David-EIPI/stm32-zigbee-light/firmware/STM32_WPAN/App/app_zigbee.c

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

/* Includes ------------------------------------------------------------------*/
#include "app_common.h"
#include "app_entry.h"
#include "dbg_trace.h"
#include "app_zigbee.h"
#include "zigbee_interface.h"
#include "shci.h"
#include "stm_logging.h"
#include "app_conf.h"
#include "stm32wbxx_core_interface_def.h"
#include "zigbee_types.h"
#include "stm32_seq.h"

#include <assert.h>
#include "zcl/zcl.h"
#include "zcl/general/zcl.temp.meas.h"
#include "zcl/general/zcl.illum.meas.h"

/* USER CODE BEGIN Includes */
#include "zcl.basic.h"
#include "main.h"
#include "hw_flash.h"
#include "ee.h"

#include "main.h"

#include "../../basic/analog.h"
#include "../../basic/binsensor.h"
#include "../../basic/multistate.h"

/* USER CODE END Includes */

#define APP_ZIGBEE_STARTUP_FAIL_DELAY               500U
#define CHANNEL                                     25

#define SW1_ENDPOINT                                1
#define SW2_ENDPOINT                                2
#define SW3_ENDPOINT                                3
#define SW4_ENDPOINT                                4
#define SW5_ENDPOINT                                5
#define SW6_ENDPOINT                                6

/* Temperature_meas (endpoint 1) specific defines ------------------------------------------------*/
#define TEMP_MIN_1                      -2000
#define TEMP_MAX_1                      5000
#define TEMP_TOLERANCE_1                      200
/* USER CODE BEGIN Temperature_meas (endpoint 1) defines */
/* USER CODE END Temperature_meas (endpoint 1) defines */

/* Illuminance_meas (endpoint 1) specific defines ------------------------------------------------*/
#define ILLUM_MIN_1                      1
#define ILLUM_MAX_1                      65534
/* USER CODE BEGIN Illuminance_meas (endpoint 1) defines */
/* USER CODE END Illuminance_meas (endpoint 1) defines */

/* USER CODE BEGIN PD */
#define CFG_NVM                 1U /* use FLASH */
#define RESET_ZB_NWK            0U

#define APP_ZIGBEE_STARTUP_REJOIN_DELAY               5000U

#define APP_ZIGBEE_REJOIN_ATTEMPTS_MAX                 2U
#define APP_ZIGBEE_TC_REJOIN_COOLDOWN_MS                60000U
#define APP_ZIGBEE_PERSIST_TIMEOUT_MS                   100000U
#define APP_ZIGBEE_DIAG_MAGIC                          0x5a424447UL /* "ZBDG" */
#define APP_ZIGBEE_DIAG_VERSION                        1U
#define APP_ZIGBEE_DIAG_WORDS                          16U
#define APP_ZIGBEE_DIAG_START_ADDR                     (CFG_EE_BANK0_MAX_NB - APP_ZIGBEE_DIAG_WORDS)
#define APP_ZIGBEE_PERSIST_CAPACITY                    ((APP_ZIGBEE_DIAG_START_ADDR * 4U) - ST_PERSIST_FLASH_DATA_OFFSET)

/* USER CODE END PD */

/* USER CODE BEGIN PM */

/* Our device is not configured as a sleepy end device, but CubeIDE still removes RXONDILE from the network setup.
 * When removed, this flag does not allow RX in idle state making Zigbee device slow to respond.
 * This macro re-definition neutralizes the auto-generated code and leaves RX always enabled.
 *
 * This hack allows to keep the project connected to the IOC file.
 *  */

#undef MCP_ASSOC_CAP_RXONIDLE
#define MCP_ASSOC_CAP_RXONIDLE 0

/*
 * Replacing the auto-generated macro with the hack below expands the channel list to all 2.4GHz channels.
 * As with the MCP_ASSOC_CAP_RXONIDLE, this hack is used to keep connection to the IOC project file.
 *  */
#undef CHANNEL
#define CHANNEL  1 ? (((1 << (26-11+1))-1) << 11) : 0
/* USER CODE END PM */

/* External definition -------------------------------------------------------*/
enum ZbStatusCodeT ZbStartupWait(struct ZigBeeT *zb, struct ZbStartupT *config);

static void APP_ZIGBEE_StackLayersInit(void);
static void APP_ZIGBEE_ConfigEndpoints(void);
static void APP_ZIGBEE_NwkForm(void);

static void APP_ZIGBEE_TraceError(const char *pMess, uint32_t ErrCode);
static void APP_ZIGBEE_CheckWirelessFirmwareInfo(void);

static void Wait_Getting_Ack_From_M0(void);
static void Receive_Ack_From_M0(void);
static void Receive_Notification_From_M0(void);

static void APP_ZIGBEE_ProcessNotifyM0ToM4(void);
static void APP_ZIGBEE_ProcessRequestM0ToM4(void);

/* USER CODE BEGIN PFP */

enum ZclStatusCodeT multistate_presentValue_CB(struct ZbZclClusterT *clusterPtr, struct ZbZclAttrCbInfoT *info);
enum ZclStatusCodeT analog_presentValue_CB(struct ZbZclClusterT *clusterPtr, struct ZbZclAttrCbInfoT *info, void *arg);

static void APP_ZIGBEE_setup_filter(void);
static void APP_ZIGBEE_ConfigBasic(void);

void set_default_attr_values(void);

static bool APP_ZIGBEE_persist_load(void);
static bool APP_ZIGBEE_persist_save(void);
static void APP_ZIGBEE_persist_delete(void);
static void APP_ZIGBEE_persist_notify_cb(struct ZigBeeT *zb, void *cbarg);
static enum ZbStatusCodeT APP_ZIGBEE_ZbStartupPersist(struct ZigBeeT *zb);
static void APP_ZIGBEE_PersistCompleted_callback(enum ZbStatusCodeT status,void *arg);
static void APP_ZIGBEE_RecoveryTask(void);
static void APP_ZIGBEE_request_recovery(uint32_t event);
static void APP_ZIGBEE_request_trust_center_rejoin(void);
static void APP_ZIGBEE_TrustCenterRejoinCompleted_callback(enum ZbStatusCodeT status, void *arg);
static void APP_ZIGBEE_mark_joined(void);
static void APP_ZIGBEE_start_coordinator_probe(void);
static void APP_ZIGBEE_CoordinatorProbeCompleted_callback(struct ZbZdoNodeDescRspT *rsp, void *arg);
static void APP_ZIGBEE_diag_record(uint32_t event, uint32_t status, uint16_t short_addr);
static bool APP_ZIGBEE_diag_load(void);
static bool APP_ZIGBEE_diag_save(void);
static uint32_t APP_ZIGBEE_crc32_update(uint32_t crc, const void *data, size_t len);


#ifdef CFG_NVM
static void APP_ZIGBEE_NVM_Init(void);
static bool APP_ZIGBEE_NVM_Read(void);
static bool APP_ZIGBEE_NVM_Write(void);
static void APP_ZIGBEE_NVM_Erase(void);
#endif /* CFG_NVM */
/* USER CODE END PFP */

static TL_CmdPacket_t   *p_ZIGBEE_otcmdbuffer;
static TL_EvtPacket_t   *p_ZIGBEE_notif_M0_to_M4;
static TL_EvtPacket_t   *p_ZIGBEE_request_M0_to_M4;
static __IO uint32_t    CptReceiveNotifyFromM0 = 0;
static __IO uint32_t    CptReceiveRequestFromM0 = 0;

PLACE_IN_SECTION("MB_MEM1") ALIGN(4) static TL_ZIGBEE_Config_t ZigbeeConfigBuffer;
PLACE_IN_SECTION("MB_MEM2") ALIGN(4) static TL_CmdPacket_t ZigbeeOtCmdBuffer;
PLACE_IN_SECTION("MB_MEM2") ALIGN(4) static uint8_t ZigbeeNotifRspEvtBuffer[sizeof(TL_PacketHeader_t) + TL_EVT_HDR_SIZE + 255U];
PLACE_IN_SECTION("MB_MEM2") ALIGN(4) static uint8_t ZigbeeNotifRequestBuffer[sizeof(TL_PacketHeader_t) + TL_EVT_HDR_SIZE + 255U];

struct zigbee_app_info
{
  bool has_init;
  struct ZigBeeT *zb;
  enum ZbStartType startupControl;
  enum ZbStatusCodeT join_status;
  uint32_t join_delay;
  bool init_after_join;

  struct ZbZclClusterT *temperature_meas_server_1;
  struct ZbZclClusterT *illuminance_meas_server_1;
};
static struct zigbee_app_info zigbee_app_info;

/* USER CODE BEGIN PV */

/* NVM variables */

static unsigned int persistNumWrites = 0;

enum app_zigbee_recovery_state {
	APP_ZIGBEE_RECOVERY_BOOT,
	APP_ZIGBEE_RECOVERY_PERSIST_PENDING,
	APP_ZIGBEE_RECOVERY_JOINED,
	APP_ZIGBEE_RECOVERY_PROBE_PENDING,
	APP_ZIGBEE_RECOVERY_REJOIN_REQUESTED,
	APP_ZIGBEE_RECOVERY_REJOIN_PENDING,
	APP_ZIGBEE_RECOVERY_FRESH_JOIN_REQUESTED,
	APP_ZIGBEE_RECOVERY_FRESH_JOIN_PENDING,
	APP_ZIGBEE_RECOVERY_TC_REJOIN_REQUESTED,
	APP_ZIGBEE_RECOVERY_TC_REJOIN_PENDING,
};

enum app_zigbee_diag_event {
	APP_ZIGBEE_DIAG_NONE,
	APP_ZIGBEE_DIAG_PERSIST_ACCEPTED,
	APP_ZIGBEE_DIAG_PERSIST_COMPLETE,
	APP_ZIGBEE_DIAG_PERSIST_FAILED,
	APP_ZIGBEE_DIAG_LEAVE,
	APP_ZIGBEE_DIAG_NETWORK_STATUS,
	APP_ZIGBEE_DIAG_REJOIN_STARTED,
	APP_ZIGBEE_DIAG_REJOIN_COMPLETE,
	APP_ZIGBEE_DIAG_FRESH_JOIN_STARTED,
	APP_ZIGBEE_DIAG_FRESH_JOIN_COMPLETE,
	APP_ZIGBEE_DIAG_PROBE_STARTED,
	APP_ZIGBEE_DIAG_PROBE_COMPLETE,
	APP_ZIGBEE_DIAG_TC_REJOIN_STARTED,
	APP_ZIGBEE_DIAG_TC_REJOIN_COMPLETE,
};

struct app_zigbee_diag_record {
	uint32_t magic;
	uint32_t version;
	uint32_t sequence;
	uint32_t last_event;
	uint32_t last_status;
	uint32_t last_short_addr;
	uint32_t persist_failures;
	uint32_t leave_events;
	uint32_t network_status_events;
	uint32_t recovery_attempts;
	uint32_t successful_recoveries;
	uint32_t last_persist_status;
	uint32_t last_leave_short_addr;
	uint32_t last_network_status;
	uint32_t last_network_short_addr;
	uint32_t crc32;
};

static struct app_zigbee_diag_record zigbee_diag;
static enum app_zigbee_recovery_state recovery_state = APP_ZIGBEE_RECOVERY_BOOT;
static bool persist_record_present;
static bool persist_record_valid;
static bool nvm_ready;
static bool diag_dirty;
static bool persist_reference_valid;
static uint16_t persist_reference_words;
static unsigned int persistNumWordsWritten;
static uint8_t rejoin_attempts;
static uint8_t trust_center_rejoin_attempts;
static uint32_t last_trust_center_rejoin_tick;
static uint64_t local_extended_address;

/* cache in uninit RAM to store/retrieve persistent data */
union cache
{
  uint8_t  U8_data[ST_PERSIST_MAX_ALLOC_SZ];     // in bytes
  uint32_t U32_data[ST_PERSIST_MAX_ALLOC_SZ/4U]; // in U32 words
};

union cache cache_persistent_data;
union cache cache_diag_reference;


struct ZbZclClusterT * analog_clusters[SW6_ENDPOINT];
struct ZbZclClusterT * multistate_cluster;
struct ZbZclClusterT * binary_cluster_light_on;
struct ZbZclClusterT * binary_cluster_motion_detect;
struct ZbZclClusterT * binary_cluster_dusk_detect;

const char *opmode_state_text[] = {
		"Auto",
		"Full",
		"Dim",
		"Off"
};

struct analog_cluster_attr {
	float value;
	float minPresent, maxPresent;
	float step;
	char desc[16];
	enum analog_mode mode;
	uint16_t engUnit;
	uint16_t icon;
	int32_t *extSetting;
	void (*ext_setting_cb)(int32_t *value);
} analog_cluster_attrs[] = {
		{
				.mode = ANALOG_OUTPUT,
				.desc = "\x09" "Dim level",
				.value = 50.0,
				.minPresent = 1.0,
				.maxPresent = 100.0,
				.step = 1.0,
				.engUnit = ZCL_ENGINEERING_UNIT_PERCENT,
				.icon = ZCL_ANALOG_ICON_BRIGHTNESS_PERCENT,
				.extSetting = &dimLevel,
		},
		{
				.mode = ANALOG_OUTPUT,
				.desc = "\x0a" "Dusk level",
				.value = 70.0,
				.minPresent = 1.0,
				.maxPresent = 200.0,
				.step = 1.0,
				.engUnit = ZCL_ENGINEERING_UNIT_PERCENT,
				.icon = ZCL_ANALOG_ICON_BRIGHTNESS_PERCENT,
				.extSetting = &ambientThreshold,
		},
		{
				.mode = ANALOG_OUTPUT,
				.desc = "\x0d" "Motion detect",
				.value = 80.0,
				.minPresent = 0.0,
				.maxPresent = 100.0,
				.step = 1.0,
				.engUnit = ZCL_ENGINEERING_UNIT_PERCENT,
				.icon = ZCL_ANALOG_ICON_PERCENT,
				.extSetting = &motionSensitivity,
				.ext_setting_cb = update_motion_sensitivity,
		},
		{
				.mode = ANALOG_OUTPUT,
				.desc = "\x0c" "After motion",
				.value = 300.0,
				.minPresent = 0.0,
				.maxPresent = 2*3600.0,
				.step = 1.0,
				.engUnit = ZCL_ENGINEERING_UNIT_SECONDS,
				.icon = ZCL_ANALOG_ICON_TIMER,
				.extSetting = &motionLight,
		},
		{
				.mode = ANALOG_OUTPUT,
				.desc = "\x0c" "After dusk",
				.value = 0.0,
				.minPresent = 1.0,
				.maxPresent = 12*60.0,
				.step = 1.0,
				.engUnit = ZCL_ENGINEERING_UNIT_MINUTES,
				.icon = ZCL_ANALOG_ICON_TIMER,
				.extSetting = &nightLight,
		},
		{
				.mode = ANALOG_OUTPUT,
				.desc = "\x0d" "Phase correct",
				.value = -300,
				.minPresent = -10000.0,
				.maxPresent = 10000,
				.step = 1,
				.engUnit = ZCL_ENGINEERING_UNIT_MICROSECONDS,
				.icon = ZCL_ANALOG_ICON_TIMER,
				.extSetting = &phase_correction,
		},
};

/* Stored attributes' values */
static uint8_t lightState = 0;
static uint8_t motionState = 0;
static uint8_t duskState = 0;

/* Data block for NVM storage */
struct persistence_attrs_v1 {
	uint32_t struct_len;
	float analogValues[lengthof(analog_cluster_attrs)];
	uint32_t multistateValue;
};

struct persistence_attrs {
	uint32_t struct_len;
	uint32_t crc32;
	float analogValues[lengthof(analog_cluster_attrs)];
	uint32_t multistateValue;
};



/* USER CODE END PV */
/* Functions Definition ------------------------------------------------------*/

/**
 * @brief  Zigbee application initialization
 * @param  None
 * @retval None
 */
void APP_ZIGBEE_Init(void)
{
  SHCI_CmdStatus_t ZigbeeInitStatus;

  APP_DBG("APP_ZIGBEE_Init");

  /* Check the compatibility with the Coprocessor Wireless Firmware loaded */
  APP_ZIGBEE_CheckWirelessFirmwareInfo();

  /* Register cmdbuffer */
  APP_ZIGBEE_RegisterCmdBuffer(&ZigbeeOtCmdBuffer);

  /* Init config buffer and call TL_ZIGBEE_Init */
  APP_ZIGBEE_TL_INIT();

  /* Register task */
  /* Create the different tasks */
  UTIL_SEQ_RegTask(1U << (uint32_t)CFG_TASK_NOTIFY_FROM_M0_TO_M4, UTIL_SEQ_RFU, APP_ZIGBEE_ProcessNotifyM0ToM4);
  UTIL_SEQ_RegTask(1U << (uint32_t)CFG_TASK_REQUEST_FROM_M0_TO_M4, UTIL_SEQ_RFU, APP_ZIGBEE_ProcessRequestM0ToM4);

  /* Task associated with network creation process */
  UTIL_SEQ_RegTask(1U << CFG_TASK_ZIGBEE_NETWORK_FORM, UTIL_SEQ_RFU, APP_ZIGBEE_NwkForm);

  /* USER CODE BEGIN APP_ZIGBEE_INIT */
//  UTIL_SEQ_RegTask(1U << CFG_TASK_ZIGBEE_NETWORK_REJOIN, UTIL_SEQ_RFU, APP_ZIGBEE_NwkRejoin);
  UTIL_SEQ_RegTask(1U << CFG_TASK_ZIGBEE_RECOVERY, UTIL_SEQ_RFU, APP_ZIGBEE_RecoveryTask);

  /* NVM Init */
#if CFG_NVM
  APP_ZIGBEE_NVM_Init();
#endif

  /* USER CODE END APP_ZIGBEE_INIT */

  /* Start the Zigbee on the CPU2 side */
  ZigbeeInitStatus = SHCI_C2_ZIGBEE_Init();
  /* Prevent unused argument(s) compilation warning */
  UNUSED(ZigbeeInitStatus);

  /* Initialize Zigbee stack layers */
  APP_ZIGBEE_StackLayersInit();

}

/**
 * @brief  Initialize Zigbee stack layers
 * @param  None
 * @retval None
 */
static void APP_ZIGBEE_StackLayersInit(void)
{
  APP_DBG("APP_ZIGBEE_StackLayersInit");

  zigbee_app_info.zb = ZbInit(0U, NULL, NULL);
  assert(zigbee_app_info.zb != NULL);

  /* Create the endpoint and cluster(s) */
  APP_ZIGBEE_ConfigEndpoints();

  /* USER CODE BEGIN APP_ZIGBEE_StackLayersInit */
  zigbee_app_info.join_status = (enum ZbStatusCodeT) 0x01; /* init to error status */
  APP_ZIGBEE_setup_filter();
  local_extended_address = ZbExtendedAddress(zigbee_app_info.zb);

  /* STEP 1 - TRY to START FROM PERSISTENCE */
  enum ZbStatusCodeT status;

  /* First we disable the persistent notification */
  ZbPersistNotifyRegister(zigbee_app_info.zb,NULL,NULL);

  /* Increase transmission power (to 3.7dbm). Default setting is 0. */
  ZbNwkIfSetTxPower(zigbee_app_info.zb, "wpan0", 6);
  enum ZbStatusCodeT res;

  /* Remove parent link strength threshold. This application does not transmit frequent data
   * and association happens faster when more nodes are available.  */
  uint32_t bdb_flags = 0;
  res = ZbBdbGetIndex(zigbee_app_info.zb, ZB_BDB_Flags, &bdb_flags, sizeof(bdb_flags), 0);
  if (ZB_STATUS_SUCCESS == res) {
	  bdb_flags |= ZB_BDB_FLAG_IGNORE_COST_DURING_JOIN;
	  (void)ZbBdbSetIndex(zigbee_app_info.zb, ZB_BDB_Flags, &bdb_flags, sizeof(bdb_flags), 0);
  }


  /* Call a startup from persistence */
#if CFG_NVM
#if (RESET_ZB_NWK)
  APP_ZIGBEE_persist_delete();
#endif
#endif

  status = APP_ZIGBEE_ZbStartupPersist(zigbee_app_info.zb);
  if(status == ZB_STATUS_SUCCESS)
  {
     /* The return value only means that CPU2 accepted the asynchronous request.
      * Network state is marked joined by APP_ZIGBEE_PersistCompleted_callback(). */
     APP_DBG("ZbStartupPersist: request accepted; waiting for completion");
     recovery_state = APP_ZIGBEE_RECOVERY_PERSIST_PENDING;
     zigbee_app_info.has_init = true;
     APP_ZIGBEE_diag_record(APP_ZIGBEE_DIAG_PERSIST_ACCEPTED, status, 0xffffU);
     return;
  }
  else
  {
       APP_DBG("ZbStartupPersist: request rejected with status: 0x%02x",status);
       if (persist_record_present) {
         APP_ZIGBEE_diag_record(APP_ZIGBEE_DIAG_PERSIST_FAILED, status, 0xffffU);
         APP_ZIGBEE_request_recovery(APP_ZIGBEE_DIAG_PERSIST_FAILED);
         zigbee_app_info.has_init = true;
         return;
       }
  }
  /* USER CODE END APP_ZIGBEE_StackLayersInit */

  /* Configure the joining parameters */
  zigbee_app_info.join_status = (enum ZbStatusCodeT) 0x01; /* init to error status */
  zigbee_app_info.join_delay = HAL_GetTick(); /* now */
  zigbee_app_info.startupControl = ZbStartTypeJoin;

  /* Initialization Complete */
  zigbee_app_info.has_init = true;

  /* run the task */
  UTIL_SEQ_SetTask(1U << CFG_TASK_ZIGBEE_NETWORK_FORM, CFG_SCH_PRIO_0);
}

/**
 * @brief  Configure Zigbee application endpoints
 * @param  None
 * @retval None
 */
static void APP_ZIGBEE_ConfigEndpoints(void)
{
  struct ZbApsmeAddEndpointReqT req;
  struct ZbApsmeAddEndpointConfT conf;

  memset(&req, 0, sizeof(req));

  /* Endpoint: SW1_ENDPOINT */
  req.profileId = ZCL_PROFILE_HOME_AUTOMATION;
  req.deviceId = ZCL_DEVICE_LEVEL_OUTPUT;
  req.endpoint = SW1_ENDPOINT;
  ZbZclAddEndpoint(zigbee_app_info.zb, &req, &conf);
  assert(conf.status == ZB_STATUS_SUCCESS);

  /* Temperature meas server */
  zigbee_app_info.temperature_meas_server_1 = ZbZclTempMeasServerAlloc(zigbee_app_info.zb, SW1_ENDPOINT, TEMP_MIN_1, TEMP_MAX_1, TEMP_TOLERANCE_1);
  assert(zigbee_app_info.temperature_meas_server_1 != NULL);
  ZbZclClusterEndpointRegister(zigbee_app_info.temperature_meas_server_1);
  /* Illuminance meas server */
  zigbee_app_info.illuminance_meas_server_1 = ZbZclIllumMeasServerAlloc(zigbee_app_info.zb, SW1_ENDPOINT, ILLUM_MIN_1, ILLUM_MAX_1);
  assert(zigbee_app_info.illuminance_meas_server_1 != NULL);
  ZbZclClusterEndpointRegister(zigbee_app_info.illuminance_meas_server_1);
  /* Endpoint: SW2_ENDPOINT */
  req.profileId = ZCL_PROFILE_HOME_AUTOMATION;
  req.deviceId = ZCL_DEVICE_LEVEL_OUTPUT;
  req.endpoint = SW2_ENDPOINT;
  ZbZclAddEndpoint(zigbee_app_info.zb, &req, &conf);
  assert(conf.status == ZB_STATUS_SUCCESS);

  /* Endpoint: SW3_ENDPOINT */
  req.profileId = ZCL_PROFILE_HOME_AUTOMATION;
  req.deviceId = ZCL_DEVICE_LEVEL_OUTPUT;
  req.endpoint = SW3_ENDPOINT;
  ZbZclAddEndpoint(zigbee_app_info.zb, &req, &conf);
  assert(conf.status == ZB_STATUS_SUCCESS);

  /* Endpoint: SW4_ENDPOINT */
  req.profileId = ZCL_PROFILE_HOME_AUTOMATION;
  req.deviceId = ZCL_DEVICE_LEVEL_OUTPUT;
  req.endpoint = SW4_ENDPOINT;
  ZbZclAddEndpoint(zigbee_app_info.zb, &req, &conf);
  assert(conf.status == ZB_STATUS_SUCCESS);

  /* Endpoint: SW5_ENDPOINT */
  req.profileId = ZCL_PROFILE_HOME_AUTOMATION;
  req.deviceId = ZCL_DEVICE_LEVEL_OUTPUT;
  req.endpoint = SW5_ENDPOINT;
  ZbZclAddEndpoint(zigbee_app_info.zb, &req, &conf);
  assert(conf.status == ZB_STATUS_SUCCESS);

  /* Endpoint: SW6_ENDPOINT */
  req.profileId = ZCL_PROFILE_HOME_AUTOMATION;
  req.deviceId = ZCL_DEVICE_ONOFF_SWITCH;
  req.endpoint = SW6_ENDPOINT;
  ZbZclAddEndpoint(zigbee_app_info.zb, &req, &conf);
  assert(conf.status == ZB_STATUS_SUCCESS);

  /* USER CODE BEGIN CONFIG_ENDPOINT */
  struct zcl_msv_attr_callbacks_t cb = {
		  .msv_presentValue = multistate_presentValue_CB,
  };
  multistate_cluster = ZbZcl_msv_ServerAlloc(zigbee_app_info.zb, SW1_ENDPOINT, MULTISTATE_VALUE,
		  lengthof(opmode_state_text), opmode_state_text, &cb, NULL);
  assert(multistate_cluster != NULL);

  char *msv_desc = "\x09" "Operation";
  (void)ZbZclAttrStringWriteShort(multistate_cluster, ZCL_MULTISTATE_DESCRIPTION_ATTR, (uint8_t*)msv_desc);

  ZbZclClusterEndpointRegister(multistate_cluster);

  unsigned ep_idx;
  for (ep_idx = SW1_ENDPOINT; ep_idx <= SW6_ENDPOINT; ep_idx += 1) {
	  unsigned cl_idx = ep_idx - 1;
	  struct zcl_analog_attr_callbacks_t analog_cb = {
			  .read = NULL,
			  .write = analog_presentValue_CB,
	  };

	  analog_clusters[cl_idx] = ZbZcl_Analog_ServerAlloc(
			  zigbee_app_info.zb,
			  ep_idx,
			  analog_cluster_attrs[cl_idx].mode,
			  &analog_cluster_attrs[cl_idx].value,
			  &analog_cb,
			  &analog_cluster_attrs[cl_idx]);

	  assert(analog_clusters[cl_idx] != NULL);

	  (void)ZbZclAttrFloatWrite(analog_clusters[cl_idx], ZCL_ANALOG_PRESENT_VALUE_ATTR, analog_cluster_attrs[cl_idx].value);
	  (void)ZbZclAttrFloatWrite(analog_clusters[cl_idx], ZCL_ANALOG_MAX_PRESENT_ATTR, analog_cluster_attrs[cl_idx].maxPresent);
	  (void)ZbZclAttrFloatWrite(analog_clusters[cl_idx], ZCL_ANALOG_MIN_PRESENT_ATTR, analog_cluster_attrs[cl_idx].minPresent);
	  (void)ZbZclAttrFloatWrite(analog_clusters[cl_idx], ZCL_ANALOG_RESOLUTION_ATTR, analog_cluster_attrs[cl_idx].step);
	  (void)ZbZclAttrIntegerWrite(analog_clusters[cl_idx], ZCL_ANALOG_ENGINEERING_UNITS_ATTR, analog_cluster_attrs[cl_idx].engUnit);
	  (void)ZbZclAttrIntegerWrite(analog_clusters[cl_idx], ZCL_ANALOG_APPLICATION_TYPE_ATTR, analog_cluster_attrs[cl_idx].icon << 16);
	  (void)ZbZclAttrStringWriteShort(analog_clusters[cl_idx], ZCL_ANALOG_DESCRIPTION_ATTR, (uint8_t*)analog_cluster_attrs[cl_idx].desc);
	  ZbZclClusterEndpointRegister(analog_clusters[cl_idx]);
  }

  binary_cluster_light_on = ZbZcl_Binary_ServerAlloc(zigbee_app_info.zb, SW1_ENDPOINT, BINARY_SENSOR_INPUT,
		  &lightState, NULL, NULL);
  assert(binary_cluster_light_on != NULL);
  ZbZclClusterEndpointRegister(binary_cluster_light_on);

  uint8_t light_on_sensor_desc[] = "\x0b" "Light state";
  (void)ZbZclAttrStringWriteShort(binary_cluster_light_on, ZCL_BINARY_DESCRIPTION_ATTR, light_on_sensor_desc);


  binary_cluster_dusk_detect = ZbZcl_Binary_ServerAlloc(zigbee_app_info.zb, SW2_ENDPOINT, BINARY_SENSOR_INPUT,
		  &duskState, NULL, NULL);
  assert(binary_cluster_dusk_detect != NULL);

  ZbZclClusterEndpointRegister(binary_cluster_dusk_detect);

  uint8_t dusk_detect_sensor_desc[] = "\x0b" "Dusk detect";
  (void)ZbZclAttrStringWriteShort(binary_cluster_dusk_detect, ZCL_BINARY_DESCRIPTION_ATTR, dusk_detect_sensor_desc);

  binary_cluster_motion_detect = ZbZcl_Binary_ServerAlloc(zigbee_app_info.zb, SW3_ENDPOINT, BINARY_SENSOR_INPUT,
		  &motionState, NULL, NULL);
  assert(binary_cluster_motion_detect != NULL);

  uint8_t motion_detect_sensor_desc[] = "\x0d" "Motion detect";
  (void)ZbZclAttrStringWriteShort(binary_cluster_motion_detect, ZCL_BINARY_DESCRIPTION_ATTR, motion_detect_sensor_desc);

  ZbZclClusterEndpointRegister(binary_cluster_motion_detect);

#if (!USE_TRAILING_EDGE)
/* This section is disabled because the current triac control is not compatible with the trailing edge drive mode */
  binary_triac_mode_cluster = ZbZcl_Binary_ServerAlloc(zigbee_app_info.zb, SW1_ENDPOINT, BINARY_SENSOR_OUTPUT,
		  &trailing_edge, NULL, NULL);
  assert(binary_triac_mode_cluster != NULL);
  ZbZclClusterEndpointRegister(binary_triac_mode_cluster);

  uint8_t triac_mode_desc[] = "\x0d" "Trailing edge";
  (void)ZbZclAttrStringWriteShort(binary_triac_mode_cluster, ZCL_BINARY_DESCRIPTION_ATTR, triac_mode_desc);
#endif

  APP_ZIGBEE_ConfigBasic();
  set_default_attr_values();
  /* USER CODE END CONFIG_ENDPOINT */
}

/**
 * @brief  Handle Zigbee network forming and joining
 * @param  None
 * @retval None
 */
static void APP_ZIGBEE_NwkForm(void)
{
  if ((zigbee_app_info.join_status != ZB_STATUS_SUCCESS) && (HAL_GetTick() >= zigbee_app_info.join_delay))
  {
    struct ZbStartupT config;
    enum ZbStatusCodeT status;

    /* Configure Zigbee Logging */
    ZbSetLogging(zigbee_app_info.zb, ZB_LOG_MASK_LEVEL_5, NULL);

    /* Attempt to join a zigbee network */
    ZbStartupConfigGetProDefaults(&config);

    /* Set the centralized network */
    APP_DBG("Network config : APP_STARTUP_CENTRALIZED_ROUTER");
    config.startupControl = zigbee_app_info.startupControl;

    /* Using the default HA preconfigured Link Key */
    memcpy(config.security.preconfiguredLinkKey, sec_key_ha, ZB_SEC_KEYSIZE);

    config.channelList.count = 1;
    config.channelList.list[0].page = 0;
    config.channelList.list[0].channelMask = 1 << CHANNEL; /*Channel in use */

    /* Using ZbStartupWait (blocking) */
    status = ZbStartupWait(zigbee_app_info.zb, &config);

    APP_DBG("ZbStartup Callback (status = 0x%02x)", status);
    zigbee_app_info.join_status = status;

    if (status == ZB_STATUS_SUCCESS)
    {
      zigbee_app_info.join_delay = 0U;
      zigbee_app_info.init_after_join = true;
      APP_DBG("Startup done !\n");
      /* USER CODE BEGIN 0 */

#if CFG_NVM
      /* Register Persistent data change notification */
      ZbPersistNotifyRegister(zigbee_app_info.zb,APP_ZIGBEE_persist_notify_cb,NULL);
      /* Call the callback once here to save persistence data */
      APP_ZIGBEE_persist_notify_cb(zigbee_app_info.zb,NULL);
#endif
      recovery_state = APP_ZIGBEE_RECOVERY_JOINED;
      rejoin_attempts = 0U;
      APP_ZIGBEE_diag_record(APP_ZIGBEE_DIAG_FRESH_JOIN_COMPLETE, status, ZbShortAddress(zigbee_app_info.zb));
      zigbee_diag.successful_recoveries++;
      diag_dirty = true;
      UTIL_SEQ_SetTask(1U << CFG_TASK_ZIGBEE_RECOVERY, CFG_SCH_PRIO_0);
      ZbZclAttrReportKick(multistate_cluster, true, NULL, NULL);
      /* Use an absolute value. Multiplying the current value after every
       * recovery caused exponential growth and eventual integer overflow. */
      uint32_t pers_tm = APP_ZIGBEE_PERSIST_TIMEOUT_MS;
      (void)ZbBdbSetIndex(zigbee_app_info.zb, ZB_BDB_PersistTimeoutMs,
		      &pers_tm, sizeof(pers_tm), 0);

      /* USER CODE END 0 */
    }
    else
    {
      APP_DBG("Startup failed, attempting again after a short delay (%d ms)", APP_ZIGBEE_STARTUP_FAIL_DELAY);
      zigbee_app_info.join_delay = HAL_GetTick() + APP_ZIGBEE_STARTUP_FAIL_DELAY;
      /* USER CODE BEGIN 1 */
      if (status != ZB_NWK_STATUS_NO_NETWORKS) {
	  zigbee_app_info.join_delay = HAL_GetTick() + APP_ZIGBEE_STARTUP_REJOIN_DELAY;
      }
      if (status == ZB_NWK_STATUS_INVALID_REQUEST || ZB_APS_STATUS_SECURITY_FAIL == status) {
    	  /* Some router devices return these error codes during first join and M0 firmware becomes
    	   * unable to join after that. It keeps sending same data and receives same error code
    	   * over and over again.
    	   * Restarting the joining process with ZbReset() seems to help most of the time. */
	  ZbReset(zigbee_app_info.zb);
      }
      recovery_state = APP_ZIGBEE_RECOVERY_FRESH_JOIN_PENDING;
      APP_ZIGBEE_diag_record(APP_ZIGBEE_DIAG_FRESH_JOIN_COMPLETE, status, 0xffffU);

      /* USER CODE END 1 */
    }
  }

  /* If Network forming/joining was not successful reschedule the current task to retry the process */
  if (zigbee_app_info.join_status != ZB_STATUS_SUCCESS)
  {
    UTIL_SEQ_SetTask(1U << CFG_TASK_ZIGBEE_NETWORK_FORM, CFG_SCH_PRIO_0);
  }
  /* USER CODE BEGIN NW_FORM */
  if (diag_dirty) {
	  UTIL_SEQ_SetTask(1U << CFG_TASK_ZIGBEE_RECOVERY, CFG_SCH_PRIO_0);
  }
  /* USER CODE END NW_FORM */
}

/*************************************************************
 * ZbStartupWait Blocking Call
 *************************************************************/
struct ZbStartupWaitInfo
{
  bool active;
  enum ZbStatusCodeT status;
};

static void ZbStartupWaitCb(enum ZbStatusCodeT status, void *cb_arg)
{
  struct ZbStartupWaitInfo *info = cb_arg;

  info->status = status;
  info->active = false;
  UTIL_SEQ_SetEvt(EVENT_ZIGBEE_STARTUP_ENDED);
}

enum ZbStatusCodeT ZbStartupWait(struct ZigBeeT *zb, struct ZbStartupT *config)
{
  struct ZbStartupWaitInfo *info;
  enum ZbStatusCodeT status;

  info = malloc(sizeof(struct ZbStartupWaitInfo));
  if (info == NULL)
  {
    return ZB_STATUS_ALLOC_FAIL;
  }
  memset(info, 0, sizeof(struct ZbStartupWaitInfo));

  info->active = true;
  status = ZbStartup(zb, config, ZbStartupWaitCb, info);
  if (status != ZB_STATUS_SUCCESS)
  {
    free(info);
    return status;
  }

  UTIL_SEQ_WaitEvt(EVENT_ZIGBEE_STARTUP_ENDED);
  status = info->status;
  free(info);
  return status;
}

/**
 * @brief  Trace the error or the warning reported.
 * @param  ErrId :
 * @param  ErrCode
 * @retval None
 */
void APP_ZIGBEE_Error(uint32_t ErrId, uint32_t ErrCode)
{
  switch (ErrId)
  {
    default:
      APP_ZIGBEE_TraceError("ERROR Unknown ", 0);
      break;
  }
}

/*************************************************************
 *
 * LOCAL FUNCTIONS
 *
 *************************************************************/

/**
 * @brief  Warn the user that an error has occurred.
 *
 * @param  pMess  : Message associated to the error.
 * @param  ErrCode: Error code associated to the module (Zigbee or other module if any)
 * @retval None
 */
static void APP_ZIGBEE_TraceError(const char *pMess, uint32_t ErrCode)
{
  APP_DBG("**** Fatal error = %s (Err = %d)", pMess, ErrCode);
}

/**
 * @brief Check if the Coprocessor Wireless Firmware loaded supports Zigbee
 *        and display associated information
 * @param  None
 * @retval None
 */
static void APP_ZIGBEE_CheckWirelessFirmwareInfo(void)
{
  WirelessFwInfo_t wireless_info_instance;
  WirelessFwInfo_t *p_wireless_info = &wireless_info_instance;

  if (SHCI_GetWirelessFwInfo(p_wireless_info) != SHCI_Success)
  {
    APP_ZIGBEE_Error((uint32_t)ERR_ZIGBEE_CHECK_WIRELESS, (uint32_t)ERR_INTERFACE_FATAL);
  }
  else
  {
    APP_DBG("**********************************************************");
    APP_DBG("WIRELESS COPROCESSOR FW:");
    /* Print version */
    APP_DBG("VERSION ID = %d.%d.%d", p_wireless_info->VersionMajor, p_wireless_info->VersionMinor, p_wireless_info->VersionSub);

    switch (p_wireless_info->StackType)
    {
      case INFO_STACK_TYPE_ZIGBEE_FFD:
        APP_DBG("FW Type : FFD Zigbee stack");
        break;

      case INFO_STACK_TYPE_ZIGBEE_RFD:
        APP_DBG("FW Type : RFD Zigbee stack");
        break;

      default:
        /* No Zigbee device supported ! */
        APP_ZIGBEE_Error((uint32_t)ERR_ZIGBEE_CHECK_WIRELESS, (uint32_t)ERR_INTERFACE_FATAL);
        break;
    }

    /* print the application name */
    char *__PathProject__ = (strstr(__FILE__, "Zigbee") ? strstr(__FILE__, "Zigbee") + 7 : __FILE__);
    char *pdel = NULL;
    if((strchr(__FILE__, '/')) == NULL)
    {
      pdel = strchr(__PathProject__, '\\');
    }
    else
    {
      pdel = strchr(__PathProject__, '/');
    }

    int index = (int)(pdel - __PathProject__);
    APP_DBG("Application flashed: %*.*s", index, index, __PathProject__);

    /* print channel */
    APP_DBG("Channel used: %d", CHANNEL);
    /* print Link Key */
    APP_DBG("Link Key: %.16s", sec_key_ha);
    /* print Link Key value hex */
    char Z09_LL_string[ZB_SEC_KEYSIZE*3+1];
    Z09_LL_string[0] = 0;
    for (int str_index = 0; str_index < ZB_SEC_KEYSIZE; str_index++)
    {
      sprintf(&Z09_LL_string[str_index*3], "%02x ", sec_key_ha[str_index]);
    }

    APP_DBG("Link Key value: %s", Z09_LL_string);
    /* print clusters allocated */
    APP_DBG("Clusters allocated are:");
    APP_DBG("temperature_meas Server on Endpoint %d", SW1_ENDPOINT);
    APP_DBG("illuminance_meas Server on Endpoint %d", SW1_ENDPOINT);
    APP_DBG("**********************************************************");
  }
}

/*************************************************************
 *
 * WRAP FUNCTIONS
 *
 *************************************************************/

void APP_ZIGBEE_RegisterCmdBuffer(TL_CmdPacket_t *p_buffer)
{
  p_ZIGBEE_otcmdbuffer = p_buffer;
}

Zigbee_Cmd_Request_t * ZIGBEE_Get_OTCmdPayloadBuffer(void)
{
  return (Zigbee_Cmd_Request_t *)p_ZIGBEE_otcmdbuffer->cmdserial.cmd.payload;
}

Zigbee_Cmd_Request_t * ZIGBEE_Get_OTCmdRspPayloadBuffer(void)
{
  return (Zigbee_Cmd_Request_t *)((TL_EvtPacket_t *)p_ZIGBEE_otcmdbuffer)->evtserial.evt.payload;
}

Zigbee_Cmd_Request_t * ZIGBEE_Get_NotificationPayloadBuffer(void)
{
  return (Zigbee_Cmd_Request_t *)(p_ZIGBEE_notif_M0_to_M4)->evtserial.evt.payload;
}

Zigbee_Cmd_Request_t * ZIGBEE_Get_M0RequestPayloadBuffer(void)
{
  return (Zigbee_Cmd_Request_t *)(p_ZIGBEE_request_M0_to_M4)->evtserial.evt.payload;
}

/**
 * @brief  This function is used to transfer the commands from the M4 to the M0.
 *
 * @param   None
 * @return  None
 */
void ZIGBEE_CmdTransfer(void)
{
  Zigbee_Cmd_Request_t *cmd_req = (Zigbee_Cmd_Request_t *)p_ZIGBEE_otcmdbuffer->cmdserial.cmd.payload;

  /* Zigbee OT command cmdcode range 0x280 .. 0x3DF = 352 */
  p_ZIGBEE_otcmdbuffer->cmdserial.cmd.cmdcode = 0x280U;
  /* Size = otCmdBuffer->Size (Number of OT cmd arguments : 1 arg = 32bits so multiply by 4 to get size in bytes)
   * + ID (4 bytes) + Size (4 bytes) */
  p_ZIGBEE_otcmdbuffer->cmdserial.cmd.plen = 8U + (cmd_req->Size * 4U);

  TL_ZIGBEE_SendM4RequestToM0();

  /* Wait completion of cmd */
  Wait_Getting_Ack_From_M0();
}

/**
 * @brief  This function is called when the M0+ acknowledge the fact that it has received a Cmd
 *
 *
 * @param   Otbuffer : a pointer to TL_EvtPacket_t
 * @return  None
 */
void TL_ZIGBEE_CmdEvtReceived(TL_EvtPacket_t *Otbuffer)
{
  /* Prevent unused argument(s) compilation warning */
  UNUSED(Otbuffer);

  Receive_Ack_From_M0();
}

/**
 * @brief  This function is called when notification from M0+ is received.
 *
 * @param   Notbuffer : a pointer to TL_EvtPacket_t
 * @return  None
 */
void TL_ZIGBEE_NotReceived(TL_EvtPacket_t *Notbuffer)
{
  p_ZIGBEE_notif_M0_to_M4 = Notbuffer;

  Receive_Notification_From_M0();
}

/**
 * @brief  This function is called before sending any ot command to the M0
 *         core. The purpose of this function is to be able to check if
 *         there are no notifications coming from the M0 core which are
 *         pending before sending a new ot command.
 * @param  None
 * @retval None
 */
void Pre_ZigbeeCmdProcessing(void)
{
  UTIL_SEQ_WaitEvt(EVENT_SYNCHRO_BYPASS_IDLE);
}

/**
 * @brief  This function waits for getting an acknowledgment from the M0.
 *
 * @param  None
 * @retval None
 */
static void Wait_Getting_Ack_From_M0(void)
{
  UTIL_SEQ_WaitEvt(EVENT_ACK_FROM_M0_EVT);
}

/**
 * @brief  Receive an acknowledgment from the M0+ core.
 *         Each command send by the M4 to the M0 are acknowledged.
 *         This function is called under interrupt.
 * @param  None
 * @retval None
 */
static void Receive_Ack_From_M0(void)
{
  UTIL_SEQ_SetEvt(EVENT_ACK_FROM_M0_EVT);
}

/**
 * @brief  Receive a notification from the M0+ through the IPCC.
 *         This function is called under interrupt.
 * @param  None
 * @retval None
 */
static void Receive_Notification_From_M0(void)
{
  CptReceiveNotifyFromM0++;
  UTIL_SEQ_SetTask(1U << (uint32_t)CFG_TASK_NOTIFY_FROM_M0_TO_M4, CFG_SCH_PRIO_0);
}

/**
 * @brief  This function is called when a request from M0+ is received.
 *
 * @param   Notbuffer : a pointer to TL_EvtPacket_t
 * @return  None
 */
void TL_ZIGBEE_M0RequestReceived(TL_EvtPacket_t *Reqbuffer)
{
  p_ZIGBEE_request_M0_to_M4 = Reqbuffer;

  CptReceiveRequestFromM0++;
  UTIL_SEQ_SetTask(1U << (uint32_t)CFG_TASK_REQUEST_FROM_M0_TO_M4, CFG_SCH_PRIO_0);
}

/**
 * @brief Perform initialization of TL for Zigbee.
 * @param  None
 * @retval None
 */
void APP_ZIGBEE_TL_INIT(void)
{
  ZigbeeConfigBuffer.p_ZigbeeOtCmdRspBuffer = (uint8_t *)&ZigbeeOtCmdBuffer;
  ZigbeeConfigBuffer.p_ZigbeeNotAckBuffer = (uint8_t *)ZigbeeNotifRspEvtBuffer;
  ZigbeeConfigBuffer.p_ZigbeeNotifRequestBuffer = (uint8_t *)ZigbeeNotifRequestBuffer;
  TL_ZIGBEE_Init(&ZigbeeConfigBuffer);
}

/**
 * @brief Process the messages coming from the M0.
 * @param  None
 * @retval None
 */
static void APP_ZIGBEE_ProcessNotifyM0ToM4(void)
{
  if (CptReceiveNotifyFromM0 != 0)
  {
    /* Reset counter */
    CptReceiveNotifyFromM0 = 0;
    Zigbee_CallBackProcessing();
  }
}

/**
 * @brief Process the requests coming from the M0.
 * @param  None
 * @retval None
 */
static void APP_ZIGBEE_ProcessRequestM0ToM4(void)
{
  if (CptReceiveRequestFromM0 != 0)
  {
    CptReceiveRequestFromM0 = 0;
    Zigbee_M0RequestProcessing();
  }
}

/* USER CODE BEGIN FD_LOCAL_FUNCTIONS */


/* callback function */
static enum zb_msg_filter_rc
app_msg_filter_callback(struct ZigBeeT *zb, uint32_t id, void *msg, void *arg)
{
	enum zb_msg_filter_rc res = ZB_MSG_CONTINUE;

	if (id == ZB_MSG_FILTER_LEAVE_IND) {
		struct ZbNlmeLeaveIndT *ind = msg;
		bool local_leave = (ind->deviceAddr == local_extended_address);

		zigbee_diag.leave_events++;

		/* A router receives leave indications for children and former neighbors.
		 * Only an indication naming our own EUI means this device left the network. */
		if (local_leave && !ind->rejoin) {
			APP_ZIGBEE_diag_record(APP_ZIGBEE_DIAG_LEAVE,
					ind->rejoin ? 1U : 0U, ind->shortAddr);
			APP_ZIGBEE_request_recovery(APP_ZIGBEE_DIAG_LEAVE);
		}
	}
	else if (id == ZB_MSG_FILTER_STATUS_IND) {
		struct ZbNlmeNetworkStatusIndT *ind = msg;

		zigbee_diag.network_status_events++;
		zigbee_diag.last_network_status = (uint32_t)ind->status;
		zigbee_diag.last_network_short_addr = ind->shortAddr;

		/* NWK status messages report failures for individual routed packets; they
		 * do not mean that a mains-powered router has left the network. Acting on
		 * route or parent-link failures here previously tore down a working router.
		 * BAD_KEY_SEQNUM is different: the coordinator is explicitly reporting a
		 * network-key sequence mismatch, for which the stack provides a dedicated
		 * Trust Center rejoin procedure. */
		if ((ind->shortAddr == ZB_NWK_ADDR_COORDINATOR) &&
				(ind->status == ZB_NWK_STATUS_CODE_BAD_KEY_SEQNUM)) {
			APP_ZIGBEE_request_trust_center_rejoin();
		}
	}

	return res;
}

static struct my_zb_app_data {
	struct ZbNlmeNetworkStatusIndT status;
} my_zb_app_data;

static void APP_ZIGBEE_setup_filter(void)
{
	/* callback initialization */

	struct ZigBeeT *zb = zigbee_app_info.zb;
	struct ZbMsgFilterT *filter = ZbMsgFilterRegister(zb,
			ZB_MSG_FILTER_LEAVE_IND | ZB_MSG_FILTER_STATUS_IND,
			ZB_MSG_DEFAULT_PRIO, app_msg_filter_callback, &my_zb_app_data);
	if (filter == NULL) {
		APP_DBG("Failed to register Zigbee network event filter");
	}
}

static void APP_ZIGBEE_RejoinCompleted_callback(struct ZbNlmeJoinConfT *conf, void *arg)
{
	APP_ZIGBEE_diag_record(APP_ZIGBEE_DIAG_REJOIN_COMPLETE,
			(uint32_t)conf->status, conf->nwkAddr);

	if (conf->status == ZB_STATUS_SUCCESS) {
		zigbee_diag.successful_recoveries++;
		diag_dirty = true;
		/* Rejoin may update the parent, short address, or security counters.
		 * Commit that refreshed stack state before normal notifications resume. */
		(void)APP_ZIGBEE_persist_save();
		APP_ZIGBEE_mark_joined();
		return;
	}

	if (rejoin_attempts < APP_ZIGBEE_REJOIN_ATTEMPTS_MAX) {
		/* Retry without resetting: ZbStartupRejoin is only valid while the stack
		 * still considers itself connected to the restored network. */
		recovery_state = APP_ZIGBEE_RECOVERY_REJOIN_REQUESTED;
	}
	else {
		/* A failed reachability repair must not strand an already commissioned
		 * router in fresh-join mode while permit-join is closed. Keep credentials
		 * and the restored stack state; later traffic or a reboot can recover it. */
		APP_ZIGBEE_mark_joined();
	}
	UTIL_SEQ_SetTask(1U << CFG_TASK_ZIGBEE_RECOVERY, CFG_SCH_PRIO_0);
}

static void APP_ZIGBEE_TrustCenterRejoinCompleted_callback(enum ZbStatusCodeT status, void *arg)
{
	UNUSED(arg);
	last_trust_center_rejoin_tick = HAL_GetTick();
	APP_ZIGBEE_diag_record(APP_ZIGBEE_DIAG_TC_REJOIN_COMPLETE,
			(uint32_t)status, ZbShortAddress(zigbee_app_info.zb));

	if (status == ZB_STATUS_SUCCESS) {
		zigbee_diag.successful_recoveries++;
		(void)APP_ZIGBEE_persist_save();
		APP_ZIGBEE_mark_joined();
	}
	else {
		/* Preserve the current network and allow another security repair only
		 * after the cooldown. Never turn a key mismatch into a factory reset. */
		recovery_state = APP_ZIGBEE_RECOVERY_JOINED;
		zigbee_app_info.join_status = ZB_STATUS_SUCCESS;
	}
}

static void APP_ZIGBEE_RecoveryTask(void)
{
	enum ZbStatusCodeT status;

	if (diag_dirty) {
		(void)APP_ZIGBEE_diag_save();
	}

	if (recovery_state == APP_ZIGBEE_RECOVERY_REJOIN_REQUESTED) {
		rejoin_attempts++;
		zigbee_diag.recovery_attempts++;
		APP_ZIGBEE_diag_record(APP_ZIGBEE_DIAG_REJOIN_STARTED,
				rejoin_attempts, 0xffffU);
		(void)ZbPersistNotifyRegister(zigbee_app_info.zb, NULL, NULL);
		zigbee_app_info.join_status = ZB_NWK_STATUS_NO_NETWORKS;

		status = ZbStartupRejoin(zigbee_app_info.zb,
				APP_ZIGBEE_RejoinCompleted_callback, NULL);
		if (status == ZB_STATUS_SUCCESS) {
			recovery_state = APP_ZIGBEE_RECOVERY_REJOIN_PENDING;
		}
		else if (rejoin_attempts < APP_ZIGBEE_REJOIN_ATTEMPTS_MAX) {
			APP_ZIGBEE_diag_record(APP_ZIGBEE_DIAG_REJOIN_COMPLETE,
					(uint32_t)status, 0xffffU);
			recovery_state = APP_ZIGBEE_RECOVERY_REJOIN_REQUESTED;
			UTIL_SEQ_SetTask(1U << CFG_TASK_ZIGBEE_RECOVERY, CFG_SCH_PRIO_0);
		}
		else {
			APP_ZIGBEE_diag_record(APP_ZIGBEE_DIAG_REJOIN_COMPLETE,
					(uint32_t)status, 0xffffU);
			APP_ZIGBEE_mark_joined();
		}
	}
	else if (recovery_state == APP_ZIGBEE_RECOVERY_TC_REJOIN_REQUESTED) {
		trust_center_rejoin_attempts++;
		zigbee_diag.recovery_attempts++;
		APP_ZIGBEE_diag_record(APP_ZIGBEE_DIAG_TC_REJOIN_STARTED,
				trust_center_rejoin_attempts, ZB_NWK_ADDR_COORDINATOR);
		status = ZbTrustCenterRejoin(zigbee_app_info.zb,
				APP_ZIGBEE_TrustCenterRejoinCompleted_callback, NULL);
		if (status == ZB_STATUS_SUCCESS) {
			recovery_state = APP_ZIGBEE_RECOVERY_TC_REJOIN_PENDING;
		}
		else {
			APP_ZIGBEE_TrustCenterRejoinCompleted_callback(status, NULL);
		}
	}
	else if (recovery_state == APP_ZIGBEE_RECOVERY_FRESH_JOIN_REQUESTED) {
		/* This is a normal BDB join, not a factory reset. The saved record and
		 * diagnostics remain available until a successful join supersedes them. */
		APP_ZIGBEE_diag_record(APP_ZIGBEE_DIAG_FRESH_JOIN_STARTED, 0U, 0xffffU);
		ZbReset(zigbee_app_info.zb);
		zigbee_app_info.startupControl = ZbStartTypeJoin;
		zigbee_app_info.join_status = ZB_NWK_STATUS_NO_NETWORKS;
		zigbee_app_info.join_delay = HAL_GetTick() + APP_ZIGBEE_STARTUP_REJOIN_DELAY;
		recovery_state = APP_ZIGBEE_RECOVERY_FRESH_JOIN_PENDING;
		UTIL_SEQ_SetTask(1U << CFG_TASK_ZIGBEE_NETWORK_FORM, CFG_SCH_PRIO_0);
	}

	if (diag_dirty) {
		(void)APP_ZIGBEE_diag_save();
	}
}


struct ZbStartupRejoinWaitInfo {
  bool active;
  enum ZbStatusCodeT status;
};

static void ZbStartupRejoinWaitCb(struct ZbNlmeJoinConfT *conf, void *cb_arg)
{
  struct ZbStartupRejoinWaitInfo *info = cb_arg;

  info->status = conf->status;
  info->active = false;
  UTIL_SEQ_SetEvt(EVENT_ZIGBEE_STARTUP_ENDED);
} /* ZbStartupWaitCb */

enum ZbStatusCodeT ZbStartupRejoinWait(struct ZigBeeT *zb)
{
  static struct ZbStartupRejoinWaitInfo info;
  enum ZbStatusCodeT status;

  memset(&info, 0, sizeof(struct ZbStartupRejoinWaitInfo));

  info.active = true;
  status = ZbStartupRejoin(zb, ZbStartupRejoinWaitCb, &info);
  if (status != ZB_STATUS_SUCCESS) {
    info.active = false;
    return status;
  }
  UTIL_SEQ_WaitEvt(EVENT_ZIGBEE_STARTUP_ENDED);
  status = info.status;
  return status;
} /* ZbStartupRejoinWait */


/**
 * @brief  Setup basic cluster attributes.
 * @param  None
 * @retval None
 */
static void APP_ZIGBEE_ConfigBasic(void)
{
 	uint8_t mfr_str[] = MANUFACTURER_NAME;
 	ZbZclBasicWriteDirect(zigbee_app_info.zb, SW1_ENDPOINT,
 			ZCL_BASIC_ATTR_MFR_NAME, mfr_str, sizeof(mfr_str) - 1);

 	uint8_t model_str[] = MODEL_NAME;
 	ZbZclBasicWriteDirect(zigbee_app_info.zb, SW1_ENDPOINT,
 			ZCL_BASIC_ATTR_MODEL_NAME, model_str, sizeof(model_str) - 1);

	uint8_t location_str[] = LOCATION;
	ZbZclBasicWriteDirect(zigbee_app_info.zb, SW1_ENDPOINT,
			ZCL_BASIC_ATTR_LOCATION, location_str, sizeof(location_str) - 1);

 	uint8_t power_source = 0x01; // single phase
 	ZbZclBasicWriteDirect(zigbee_app_info.zb, SW1_ENDPOINT,
 			ZCL_BASIC_ATTR_POWER_SOURCE, &power_source, 1);

 	uint8_t physical_env = 0x0c; // deck
 	ZbZclBasicWriteDirect(zigbee_app_info.zb, SW1_ENDPOINT,
 			ZCL_BASIC_ATTR_ENVIRONMENT, &physical_env, 1);
}

/**
 * @brief  Set default attribute values if not starting from persistence
 * @param  None
 * @retval None
 */
void set_default_attr_values(void)
{
	unsigned ep_idx;
	for (ep_idx = SW1_ENDPOINT; ep_idx <= SW6_ENDPOINT; ep_idx += 1) {
		unsigned cl_idx = ep_idx - 1;
		(void)ZbZclAttrFloatWrite(analog_clusters[cl_idx], ZCL_ANALOG_PRESENT_VALUE_ATTR, analog_cluster_attrs[cl_idx].value);
	}

	(void)ZbZclAttrIntegerWrite(multistate_cluster, ZCL_MULTISTATE_PRESENT_VALUE_ATTR, operationMode);
}


/**
 * @brief  Set global parameter in response to the changed attribute value
 * @param  New attribute value
 * @retval None
 */
static void multistate_set_mode(uint16_t opmode)
{
	if (opmode >= OP_AUTO && opmode <= OP_OFF) {
		operationMode = opmode;
	}

}

/**
 * @brief  Callback function for the MultistateValue cluster
 * @param  Pointer to the cluster data
 * @param  Pointer to the attribute data
 * @retval Zigbee cluster library Status code
 */
enum ZclStatusCodeT multistate_presentValue_CB(struct ZbZclClusterT *clusterPtr, struct ZbZclAttrCbInfoT *info)
{
	uint16_t attributeId = info->info->attributeId;
	uint8_t endpoint = clusterPtr->endpoint;

	if (attributeId == ZCL_MULTISTATE_PRESENT_VALUE_ATTR && endpoint == SW1_ENDPOINT ) {
			enum ZclStatusCodeT result = ZCL_STATUS_SUCCESS;
			enum ZclDataTypeT type;
			uint16_t opmode = ZbZclAttrIntegerRead(clusterPtr, attributeId, &type, &result);
			if (ZCL_STATUS_SUCCESS == result)
				multistate_set_mode(opmode);
	}
	return ZCL_STATUS_SUCCESS;
}

/**
 * @brief  Set global parameter in response to the changed attribute value. Converts float value to integer value.
 * @param  Pointer to the attribute description data
 * @retval None
 */
void update_analog_attr_setting(struct analog_cluster_attr *attr)
{
	if (attr->extSetting) {
		float step_cnt = attr->value / attr->step;
		step_cnt =	 attr->value < 0 ? step_cnt - 0.5 : step_cnt + 0.5;
		*attr->extSetting = (int32_t)step_cnt;
		if (attr->ext_setting_cb)
			attr->ext_setting_cb(attr->extSetting);
	}
}

/**
 * @brief  Set global parameter in response to the changed attribute value
 * @param  Pointer to the cluster data
 * @param  Pointer to the attribute data
 * @param  Callback argument (stores attribute description data)
 * @retval Zigbee cluster library Status code
 */
enum ZclStatusCodeT analog_presentValue_CB(struct ZbZclClusterT *clusterPtr, struct ZbZclAttrCbInfoT *info, void *arg)
{
	struct analog_cluster_attr *attr = (struct analog_cluster_attr *)arg;
	update_analog_attr_setting(attr);
	return ZCL_STATUS_SUCCESS;
}


/**
 * @brief  Update value attribute of the illuminance measurement cluster
 * @param  Illuminance measurement
 * @retval None
 */
void APP_ZIGBEE_update_illum(uint16_t illum)
{
	int ha_illum;
/*
 * We need to send 10000 * log10(I), and we have 10*log2(I) + 50, so convert here
 */
	ha_illum = ((int)illum - 50) * 301;
	if (ha_illum <= 0) ha_illum = 1;
	(void)ZbZclAttrIntegerWrite(zigbee_app_info.illuminance_meas_server_1, ZCL_ILLUM_MEAS_ATTR_MEAS_VAL, ha_illum);
}

/**
 * @brief  Update value attribute of the binary input cluster
 * @param  Light state
 * @retval None
 */
void APP_ZIGBEE_update_lightstate(uint16_t state)
{
	if ((0 == state) != (0 == lightState))
		(void)ZbZclAttrIntegerWrite(binary_cluster_light_on, ZCL_BINARY_PRESENT_VALUE_ATTR, state);
}

/**
 * @brief  Update value attribute of the binary input cluster
 * @param  Motion detect
 * @retval None
 */
void APP_ZIGBEE_update_motion_detect(uint16_t state)
{
	if ((0 == state) != (0 == motionState))
		(void)ZbZclAttrIntegerWrite(binary_cluster_motion_detect, ZCL_BINARY_PRESENT_VALUE_ATTR, state);
}

/**
 * @brief  Update value attribute of the binary input cluster
 * @param  Dusk detect
 * @retval None
 */
void APP_ZIGBEE_update_dusk_detect(uint16_t state)
{
	if ((0 == state) != (0 == duskState))
		(void)ZbZclAttrIntegerWrite(binary_cluster_dusk_detect, ZCL_BINARY_PRESENT_VALUE_ATTR, state);
}

/**
 * @brief  Update value attribute of the temperature sensor cluster
 * @param  Temperature C x 100
 * @retval None
 */
void APP_ZIGBEE_update_temperature(int16_t temp)
{
	(void)ZbZclAttrIntegerWrite(zigbee_app_info.temperature_meas_server_1, ZCL_TEMP_MEAS_ATTR_MEAS_VAL, temp);
}

static uint32_t APP_ZIGBEE_crc32_update(uint32_t crc, const void *data, size_t len)
{
	const uint8_t *bytes = data;

	while (len-- != 0U) {
		crc ^= *bytes++;
		for (unsigned bit = 0; bit < 8U; bit++) {
			crc = (crc >> 1) ^ ((crc & 1U) ? 0xedb88320UL : 0U);
		}
	}
	return crc;
}

static uint32_t APP_ZIGBEE_persist_crc(const uint8_t *stack_data, uint32_t stack_len,
		const struct persistence_attrs *attrs)
{
	struct persistence_attrs copy;
	uint32_t crc = 0xffffffffUL;

	/* The stack blob has byte granularity, so its footer is not necessarily
	 * word-aligned. Avoid compiler-generated LDM/STM instructions here. */
	memcpy(&copy, attrs, sizeof(copy));
	copy.crc32 = 0U;
	crc = APP_ZIGBEE_crc32_update(crc, stack_data, stack_len);
	crc = APP_ZIGBEE_crc32_update(crc, &copy, sizeof(copy));
	return ~crc;
}

static void APP_ZIGBEE_diag_record(uint32_t event, uint32_t status, uint16_t short_addr)
{
	bool persist_event = false;

	zigbee_diag.last_event = event;
	zigbee_diag.last_status = status;
	zigbee_diag.last_short_addr = short_addr;
	if (event == APP_ZIGBEE_DIAG_PERSIST_FAILED) {
		zigbee_diag.persist_failures++;
		zigbee_diag.last_persist_status = status;
		persist_event = true;
	}
	else if (event == APP_ZIGBEE_DIAG_LEAVE) {
		zigbee_diag.last_leave_short_addr = short_addr;
		persist_event = true;
	}
	else if (event == APP_ZIGBEE_DIAG_NETWORK_STATUS) {
		zigbee_diag.last_network_status = status;
		zigbee_diag.last_network_short_addr = short_addr;
	}
	else if ((event == APP_ZIGBEE_DIAG_REJOIN_STARTED) ||
			(event == APP_ZIGBEE_DIAG_REJOIN_COMPLETE) ||
			(event == APP_ZIGBEE_DIAG_FRESH_JOIN_STARTED) ||
			((event == APP_ZIGBEE_DIAG_FRESH_JOIN_COMPLETE) &&
			 (status == ZB_STATUS_SUCCESS)) ||
			((event == APP_ZIGBEE_DIAG_PROBE_COMPLETE) &&
			 (status != ZB_STATUS_SUCCESS)) ||
			(event == APP_ZIGBEE_DIAG_TC_REJOIN_STARTED) ||
			(event == APP_ZIGBEE_DIAG_TC_REJOIN_COMPLETE)) {
		persist_event = true;
	}

	/* Diagnostics are a crash-recovery breadcrumb, not a telemetry log. Routine
	 * status traffic and successful boots stay in RAM to avoid flash wear. */
	if (persist_event) {
		diag_dirty = true;
		UTIL_SEQ_SetTask(1U << CFG_TASK_ZIGBEE_RECOVERY, CFG_SCH_PRIO_0);
	}
}

static bool APP_ZIGBEE_diag_load(void)
{
	struct app_zigbee_diag_record record;
	uint32_t *words = (uint32_t *)&record;

	_Static_assert(sizeof(record) == APP_ZIGBEE_DIAG_WORDS * sizeof(uint32_t),
			"Diagnostic record size must match reserved EEPROM words");

	memset(&record, 0, sizeof(record));
	if (!nvm_ready) {
		return false;
	}
	for (uint16_t i = 0; i < APP_ZIGBEE_DIAG_WORDS; i++) {
		if (EE_Read(0, APP_ZIGBEE_DIAG_START_ADDR + i, &words[i]) != EE_OK) {
			return false;
		}
	}

	uint32_t stored_crc = record.crc32;
	record.crc32 = 0U;
	uint32_t crc = ~APP_ZIGBEE_crc32_update(0xffffffffUL, &record, sizeof(record));
	if ((record.magic != APP_ZIGBEE_DIAG_MAGIC) ||
			(record.version != APP_ZIGBEE_DIAG_VERSION) || (crc != stored_crc)) {
		return false;
	}

	record.crc32 = stored_crc;
	zigbee_diag = record;
	return true;
}

static bool APP_ZIGBEE_diag_save(void)
{
	uint32_t *words = (uint32_t *)&zigbee_diag;
	int status = EE_OK;

	if (!nvm_ready || !diag_dirty) {
		return !diag_dirty;
	}

	zigbee_diag.magic = APP_ZIGBEE_DIAG_MAGIC;
	zigbee_diag.version = APP_ZIGBEE_DIAG_VERSION;
	zigbee_diag.sequence++;
	zigbee_diag.crc32 = 0U;
	zigbee_diag.crc32 = ~APP_ZIGBEE_crc32_update(0xffffffffUL,
			&zigbee_diag, sizeof(zigbee_diag));

	/* Write CRC last. A reset during the preceding writes leaves a record whose
	 * old CRC cannot validate the mixed generation. */
	for (uint16_t i = 0; i < APP_ZIGBEE_DIAG_WORDS - 1U; i++) {
		status = EE_Write(0, APP_ZIGBEE_DIAG_START_ADDR + i, words[i]);
		if (status != EE_OK) {
			return false;
		}
	}
	status = EE_Write(0, APP_ZIGBEE_DIAG_START_ADDR + APP_ZIGBEE_DIAG_WORDS - 1U,
			words[APP_ZIGBEE_DIAG_WORDS - 1U]);
	if (status == EE_OK) {
		diag_dirty = false;
		return true;
	}
	return false;
}

static void APP_ZIGBEE_request_recovery(uint32_t event)
{
	if ((recovery_state == APP_ZIGBEE_RECOVERY_REJOIN_PENDING) ||
			(recovery_state == APP_ZIGBEE_RECOVERY_FRESH_JOIN_PENDING) ||
			(recovery_state == APP_ZIGBEE_RECOVERY_TC_REJOIN_PENDING)) {
		return;
	}
	rejoin_attempts = 0U;
	/* Without a successfully restored stack there is no usable network key to
	 * rejoin with. An explicit local leave likewise requires commissioning.
	 * Reachability-probe failures retain the restored network and use bounded
	 * in-network rejoin attempts. */
	if ((event == APP_ZIGBEE_DIAG_PERSIST_FAILED) ||
			(event == APP_ZIGBEE_DIAG_LEAVE)) {
		recovery_state = APP_ZIGBEE_RECOVERY_FRESH_JOIN_REQUESTED;
	}
	else {
		recovery_state = APP_ZIGBEE_RECOVERY_REJOIN_REQUESTED;
	}
	UTIL_SEQ_SetTask(1U << CFG_TASK_ZIGBEE_RECOVERY, CFG_SCH_PRIO_0);
}

static void APP_ZIGBEE_request_trust_center_rejoin(void)
{
	uint32_t now = HAL_GetTick();

	if ((recovery_state != APP_ZIGBEE_RECOVERY_JOINED) ||
			((last_trust_center_rejoin_tick != 0U) &&
			 ((uint32_t)(now - last_trust_center_rejoin_tick) <
					 APP_ZIGBEE_TC_REJOIN_COOLDOWN_MS))) {
		return;
	}
	trust_center_rejoin_attempts = 0U;
	recovery_state = APP_ZIGBEE_RECOVERY_TC_REJOIN_REQUESTED;
	APP_ZIGBEE_diag_record(APP_ZIGBEE_DIAG_NETWORK_STATUS,
			ZB_NWK_STATUS_CODE_BAD_KEY_SEQNUM, ZB_NWK_ADDR_COORDINATOR);
	UTIL_SEQ_SetTask(1U << CFG_TASK_ZIGBEE_RECOVERY, CFG_SCH_PRIO_0);
}

static void APP_ZIGBEE_mark_joined(void)
{
	uint32_t pers_tm = APP_ZIGBEE_PERSIST_TIMEOUT_MS;

	recovery_state = APP_ZIGBEE_RECOVERY_JOINED;
	rejoin_attempts = 0U;
	trust_center_rejoin_attempts = 0U;
	zigbee_app_info.join_status = ZB_STATUS_SUCCESS;
	zigbee_app_info.join_delay = 0U;
	zigbee_app_info.init_after_join = true;
	set_default_attr_values();
	(void)ZbPersistNotifyRegister(zigbee_app_info.zb, APP_ZIGBEE_persist_notify_cb, NULL);
	(void)ZbBdbSetIndex(zigbee_app_info.zb, ZB_BDB_PersistTimeoutMs,
			&pers_tm, sizeof(pers_tm), 0);
	ZbZclAttrReportKick(multistate_cluster, true, NULL, NULL);
}

static void APP_ZIGBEE_CoordinatorProbeCompleted_callback(
		struct ZbZdoNodeDescRspT *rsp, void *arg)
{
	UNUSED(arg);
	APP_ZIGBEE_diag_record(APP_ZIGBEE_DIAG_PROBE_COMPLETE,
			(uint32_t)rsp->status, rsp->nwkAddr);

	/* A network event may already have started recovery while this ZDO
	 * transaction was outstanding. Do not let a late response undo it. */
	if (recovery_state != APP_ZIGBEE_RECOVERY_PROBE_PENDING) {
		return;
	}
	if (rsp->status == ZB_STATUS_SUCCESS) {
		recovery_state = APP_ZIGBEE_RECOVERY_JOINED;
		return;
	}

	APP_ZIGBEE_request_recovery(APP_ZIGBEE_DIAG_PROBE_COMPLETE);
}

static void APP_ZIGBEE_start_coordinator_probe(void)
{
	struct ZbZdoNodeDescReqT req = {
		.dstNwkAddr = ZB_NWK_ADDR_COORDINATOR,
		.nwkAddrOfInterest = ZB_NWK_ADDR_COORDINATOR,
	};
	enum ZbStatusCodeT status;

	recovery_state = APP_ZIGBEE_RECOVERY_PROBE_PENDING;
	APP_ZIGBEE_diag_record(APP_ZIGBEE_DIAG_PROBE_STARTED, 0U,
			ZB_NWK_ADDR_COORDINATOR);
	status = ZbZdoNodeDescReq(zigbee_app_info.zb, &req,
			APP_ZIGBEE_CoordinatorProbeCompleted_callback, NULL);
	if (status != ZB_STATUS_SUCCESS) {
		APP_ZIGBEE_diag_record(APP_ZIGBEE_DIAG_PROBE_COMPLETE,
				(uint32_t)status, ZB_NWK_ADDR_COORDINATOR);
		APP_ZIGBEE_request_recovery(APP_ZIGBEE_DIAG_PROBE_COMPLETE);
	}
}


/*************************************************************
 *
 * NVM FUNCTIONS
 *
 *************************************************************/
static void APP_ZIGBEE_pack_persist_values(struct persistence_attrs *persistence_attrs,
		const uint8_t *stack_data, uint32_t stack_len)
{
	struct persistence_attrs aligned = { 0 };

	aligned.struct_len = sizeof(aligned);

    unsigned n;
    for (n = 0; n < lengthof(analog_cluster_attrs); n++)
		aligned.analogValues[n] = analog_cluster_attrs[n].value;

	aligned.multistateValue = operationMode;
	aligned.crc32 = APP_ZIGBEE_persist_crc(stack_data, stack_len, &aligned);
	memcpy(persistence_attrs, &aligned, sizeof(aligned));
}

static void APP_ZIGBEE_unpack_persist_values(struct persistence_attrs *persistence_attrs)
{
	struct persistence_attrs aligned;

	memcpy(&aligned, persistence_attrs, sizeof(aligned));
	if (aligned.struct_len == sizeof(aligned)) {
		unsigned n;
		for (n = 0; n < lengthof(analog_cluster_attrs); n++)
			analog_cluster_attrs[n].value = aligned.analogValues[n];

		operationMode = aligned.multistateValue;
	}
}

static void APP_ZIGBEE_unpack_persist_values_v1(const struct persistence_attrs_v1 *persistence_attrs)
{
	struct persistence_attrs_v1 aligned;

	memcpy(&aligned, persistence_attrs, sizeof(aligned));
	if (aligned.struct_len == sizeof(aligned)) {
		for (unsigned n = 0; n < lengthof(analog_cluster_attrs); n++) {
			analog_cluster_attrs[n].value = aligned.analogValues[n];
		}
		operationMode = aligned.multistateValue;
	}
}

/**
 * @brief  notify to save persistent data callback
 * @param  zb: Zigbee device object pointer, cbarg: callback arg pointer
 * @retval None
 */
static void APP_ZIGBEE_persist_notify_cb(struct ZigBeeT *zb, void *cbarg)
{
  APP_DBG("Notification to save persistent data requested from stack");
  /* Save the persistent data */
  APP_ZIGBEE_persist_save();
}

/**
 * @brief  Start Zigbee Network from persistent data
 * @param  zb: Zigbee device object pointer
 * @retval Zigbee stack Status code
 */
static enum ZbStatusCodeT APP_ZIGBEE_ZbStartupPersist(struct ZigBeeT* zb)
{
   bool read_status;
   enum ZbStatusCodeT status = ZB_STATUS_SUCCESS;

   /* Restore persistence */
   read_status = APP_ZIGBEE_persist_load();

   if (read_status)
   {
       /* Make sure the EPID is cleared, before we are allowed to restore persistence */
       uint64_t epid = 0U;
       ZbNwkSet(zb, ZB_NWK_NIB_ID_ExtendedPanId, &epid, sizeof(uint64_t));

       /* Start-up from persistence */
       APP_DBG("APP_ZIGBEE_ZbStartupPersist: restoring stack persistence");
       status = ZbStartupPersist(zb, &cache_persistent_data.U8_data[4], cache_persistent_data.U32_data[0],NULL,APP_ZIGBEE_PersistCompleted_callback,NULL);
   }
   else
   {
       /* Failed to restart from persistence */
       APP_DBG("APP_ZIGBEE_ZbStartupPersist: no persistence data to restore");
       status = ZB_STATUS_ALLOC_FAIL;
   }

   /* Only for debug purpose, depending of persistent data, following traces
      could display bytes that are irrelevants to on off cluster */
   if(status == ZB_STATUS_SUCCESS)
   {
     /* read the last bytes of data where the ZCL on off persistent data shall be*/
      uint32_t len = cache_persistent_data.U32_data[0] + 4 ;
      APP_DBG("ClusterID %02x %02x",cache_persistent_data.U8_data[len-9],cache_persistent_data.U8_data[len-10]);
      APP_DBG("Endpoint %02x %02x",cache_persistent_data.U8_data[len-7],cache_persistent_data.U8_data[len-8]);
      APP_DBG("Direction %02x",cache_persistent_data.U8_data[len-6]);
      APP_DBG("AttrID %02x %02x",cache_persistent_data.U8_data[len-4],cache_persistent_data.U8_data[len-5]);
      APP_DBG("Len %02x %02x",cache_persistent_data.U8_data[len-2],cache_persistent_data.U8_data[len-3]);
      APP_DBG("Value %02x",cache_persistent_data.U8_data[len-1]);
   }

   return status;
}/* APP_ZIGBEE_ZbStartupPersist */

/**
 * @brief  timer callback to wait end of restore cluster persistence form M0
 * @param  None
 * @retval None
 */
static void APP_ZIGBEE_PersistCompleted_callback(enum ZbStatusCodeT status,void *arg)
{
   if(status == ZB_WPAN_STATUS_SUCCESS)
   {
	   APP_DBG("Persist complete callback entered with SUCCESS");
	   APP_ZIGBEE_diag_record(APP_ZIGBEE_DIAG_PERSIST_COMPLETE,
			   (uint32_t)status, ZbShortAddress(zigbee_app_info.zb));
	   APP_ZIGBEE_mark_joined();
	   APP_ZIGBEE_start_coordinator_probe();
   }
   else
   {
	   APP_DBG("Error in persist complete callback %x",status);
	   APP_ZIGBEE_diag_record(APP_ZIGBEE_DIAG_PERSIST_FAILED,
			   (uint32_t)status, 0xffffU);
	   APP_ZIGBEE_request_recovery(APP_ZIGBEE_DIAG_PERSIST_FAILED);
   }
}/* APP_ZIGBEE_PersistCompleted_callback */


/**
 * @brief  Load persistent data
 * @param  None
 * @retval true if success, false if fail
 */
static bool APP_ZIGBEE_persist_load(void)
{
#ifdef CFG_NVM
    APP_DBG("Retrieving persistent data from FLASH");
    bool status = APP_ZIGBEE_NVM_Read();
	persist_record_present = status;
	persist_record_valid = false;

    if (status) {
		uint32_t total_len = cache_persistent_data.U32_data[0];

		if (total_len > sizeof(struct persistence_attrs)) {
			uint32_t stack_len = total_len - sizeof(struct persistence_attrs);
			const uint8_t *footer =
					&cache_persistent_data.U8_data[ST_PERSIST_FLASH_DATA_OFFSET + stack_len];
			struct persistence_attrs attrs;
			memcpy(&attrs, footer, sizeof(attrs));
			if ((attrs.struct_len == sizeof(attrs)) &&
					(attrs.crc32 == APP_ZIGBEE_persist_crc(
							&cache_persistent_data.U8_data[ST_PERSIST_FLASH_DATA_OFFSET],
							stack_len, &attrs))) {
				cache_persistent_data.U32_data[0] = stack_len;
				APP_ZIGBEE_unpack_persist_values(&attrs);
				persist_record_valid = true;
			}
		}

		/* Accept the previous footer format once, then convert it on the next save. */
		if (!persist_record_valid && (total_len > sizeof(struct persistence_attrs_v1))) {
			uint32_t stack_len = total_len - sizeof(struct persistence_attrs_v1);
			struct persistence_attrs_v1 attrs;
			memcpy(&attrs,
					&cache_persistent_data.U8_data[ST_PERSIST_FLASH_DATA_OFFSET + stack_len],
					sizeof(attrs));
			if (attrs.struct_len == sizeof(attrs)) {
				cache_persistent_data.U32_data[0] = stack_len;
				APP_ZIGBEE_unpack_persist_values_v1(&attrs);
				persist_record_valid = true;
			}
		}
    }
	if (persist_record_present && !persist_record_valid) {
		APP_DBG("Persistent data footer or CRC is invalid");
	}
    return persist_record_valid;
#else
    /* Check length range */
    if ((cache_persistent_data.U32_data[0] == 0) ||
        (cache_persistent_data.U32_data[0] > ST_PERSIST_MAX_ALLOC_SZ))
    {
        APP_DBG("No data or too large length : %d",cache_persistent_data.U32_data[0]);
        return false;
    }
    return true;
#endif /* CFG_NVM */
} /* APP_ZIGBEE_persist_load */

/**
 * @brief  Save persistent data
 * @param  None
 * @retval true if success , false if fail
 */
static bool APP_ZIGBEE_persist_save(void)
{
    uint32_t len;

    /* Clear the RAM cache before saving */
    memset(cache_persistent_data.U8_data, 0x00, ST_PERSIST_MAX_ALLOC_SZ);

    /* Call the stack API to get current persistent data */
    len = ZbPersistGet(zigbee_app_info.zb, 0, 0);
    /* Check Length range */
    if (len == 0U)
    {
        /* If the persistence length was zero then no data available. */
        APP_DBG("APP_ZIGBEE_persist_save: no persistence data to save !");
        return false;
    }
    if (len > APP_ZIGBEE_PERSIST_CAPACITY - sizeof(struct persistence_attrs))
    {
        /* if persistence length too big to store */
        APP_DBG("APP_ZIGBEE_persist_save: persist size too large for storage (%d)", len);
        return false;
    }

    /* Store in cache the persistent data */
    len = ZbPersistGet(zigbee_app_info.zb, &cache_persistent_data.U8_data[ST_PERSIST_FLASH_DATA_OFFSET], len);

    /* Append attribute values that need to survive restarts. ZCL persistence code is unreliable, so implement the separate storage. */
    struct persistence_attrs *persistence_attrs = (struct persistence_attrs *)&cache_persistent_data.U8_data[ST_PERSIST_FLASH_DATA_OFFSET + len];
    APP_ZIGBEE_pack_persist_values(persistence_attrs,
			&cache_persistent_data.U8_data[ST_PERSIST_FLASH_DATA_OFFSET], len);

    /* Store in cache the persistent data length */
    cache_persistent_data.U32_data[0] = len + sizeof(struct persistence_attrs);

    persistNumWrites++;
    APP_DBG("APP_ZIGBEE_persist_save: Persistence written in cache RAM (num writes = %d) len=%d",
             persistNumWrites, cache_persistent_data.U32_data[0]);

#ifdef CFG_NVM
    if(!APP_ZIGBEE_NVM_Write())
    {
    	return false;
    }

    APP_DBG("APP_ZIGBEE_persist_save: Persistent data FLASHED");
#endif /* CFG_NVM */

    return true;
} /* APP_ZIGBEE_persist_save */

/**
 * @brief  Delete persistent data
 * @param  None
 * @retval None
 */
static void APP_ZIGBEE_persist_delete(void)
{
  /* Clear RAM cache */
   memset(cache_persistent_data.U8_data, 0x00, ST_PERSIST_MAX_ALLOC_SZ);
   APP_DBG("Persistent Data RAM cache cleared");
#ifdef CFG_NVM
   APP_DBG("FLASH ERASED");
   APP_ZIGBEE_NVM_Erase();
#endif /* CFG_NVM */
} /* APP_ZIGBEE_persist_delete */


#ifdef CFG_NVM
/**
 * @brief  Init the NVM
 * @param  None
 * @retval None
 */
static void APP_ZIGBEE_NVM_Init(void)
{
  int eeprom_init_status;

  APP_DBG("Flash starting address = %x",HW_FLASH_ADDRESS  + CFG_NVM_BASE_ADDRESS);
  eeprom_init_status = EE_Init( 0 , HW_FLASH_ADDRESS + CFG_NVM_BASE_ADDRESS );

  if(eeprom_init_status != EE_OK)
  {
	/* Do not format automatically. Preserve the failed bank for field diagnosis;
	 * an explicit leave/factory-reset operation may format it later. */
	nvm_ready = false;
	APP_DBG("EE recovery failed; NVM retained for diagnosis");
	return;
  }
	nvm_ready = true;
	if (!APP_ZIGBEE_diag_load()) {
		memset(&zigbee_diag, 0, sizeof(zigbee_diag));
		zigbee_diag.magic = APP_ZIGBEE_DIAG_MAGIC;
		zigbee_diag.version = APP_ZIGBEE_DIAG_VERSION;
	}
	persist_reference_valid = false;
	persist_reference_words = 0U;
  APP_DBG("EE_init status = %d",eeprom_init_status);

} /* APP_ZIGBEE_NVM_Init */

/**
*@brief  Read the persistent data from NVM
* @param  None
* @retval true if success , false if failed
*/
static bool APP_ZIGBEE_NVM_Read(void)
{
    uint16_t num_words = 0;
    bool status = true;
    int ee_status = 0;
	persist_reference_valid = false;
	persist_reference_words = 0U;
	if (!nvm_ready) {
		return false;
	}
    HAL_FLASH_Unlock();
    __HAL_FLASH_CLEAR_FLAG(FLASH_FLAG_EOP | FLASH_FLAG_PGSERR | FLASH_FLAG_WRPERR | FLASH_FLAG_OPTVERR);

    /* Read the data length from cache */
    ee_status = EE_Read(0, ZIGBEE_DB_START_ADDR, &cache_persistent_data.U32_data[0]);
    if (ee_status != EE_OK)
    {
        APP_DBG("Read -> persistent data length not found ERASE to be done - Read Stopped");
        status = false;
    }
      /* Check length is not too big nor zero */
    else if((cache_persistent_data.U32_data[0] == 0) ||
            (cache_persistent_data.U32_data[0] > APP_ZIGBEE_PERSIST_CAPACITY))
    {
            APP_DBG("No data or too large length : %d", cache_persistent_data.U32_data[0]);
            status = false;
    }
        /* Length is within range */
    else
    {
           /* Adjust the length to be U32 aligned */
            num_words = (uint16_t) (cache_persistent_data.U32_data[0]/4) ;
            if (cache_persistent_data.U32_data[0] % 4 != 0)
            {
                num_words++;
            }

            /* copy the read data from Flash to cache including length */
            for (uint16_t local_length = 1; local_length <= num_words; local_length++)
            {
            	if (local_length >= ST_PERSIST_MAX_ALLOC_SZ/4)
            	{
                    APP_DBG("Local length exceeds the size of the cache persistent data!");
                    status = false;
                    break;
            	}

                /* read data from first data in U32 unit */
                ee_status = EE_Read(0, local_length + ZIGBEE_DB_START_ADDR, &cache_persistent_data.U32_data[local_length] );
                if (ee_status != EE_OK)
                {
                    APP_DBG("Read not found leaving");
                    status = false;
                    break;
                }
            }
    }

    HAL_FLASH_Lock();
    if(status)
    {
		/* Keep an exact RAM shadow of the committed logical EEPROM image. The
		 * persistence loader subsequently removes the application footer length
		 * from cache_persistent_data, so take the copy before returning. */
		memcpy(&cache_diag_reference, &cache_persistent_data,
				 sizeof(cache_diag_reference));
		persist_reference_words = (uint16_t)(1U +
				((cache_persistent_data.U32_data[0] + 3U) / 4U));
		persist_reference_valid = true;
        APP_DBG("READ PERSISTENT DATA LEN = %d",cache_persistent_data.U32_data[0]);
    }
    return status;
} /* APP_ZIGBEE_NVM_Read */

/**
 * @brief  Write the persistent data in NVM
 * @param  None
 * @retval None
 */
static bool APP_ZIGBEE_NVM_Write(void)
{
    int ee_status = 0;

    uint16_t num_words;
    uint16_t local_current_size;
	uint16_t words_written = 0U;


	if (!nvm_ready) {
		return false;
	}

    num_words = 1U; /* 1 words for the length */
    num_words+= (uint16_t) (cache_persistent_data.U32_data[0]/4);


    /* Adjust the length to be U32 aligned */
    if (cache_persistent_data.U32_data[0] % 4 != 0)
    {
        num_words++;
    }

    /* Program data before the length/commit word. Compare against the RAM
     * shadow rather than calling EE_Read for every word: EE_Read scans the
     * append-only pool, while a RAM comparison is constant-time. Words beyond
     * the previous image length must be written even if the shadow happens to
     * contain the same value, because an older stale virtual value may exist. */
    for (local_current_size = 1U; local_current_size < num_words; local_current_size++)
    {
		if (persist_reference_valid &&
				(local_current_size < persist_reference_words) &&
				(cache_diag_reference.U32_data[local_current_size] ==
				 cache_persistent_data.U32_data[local_current_size])) {
			continue;
		}
        ee_status = EE_Write(0, (uint16_t)local_current_size + ZIGBEE_DB_START_ADDR, cache_persistent_data.U32_data[local_current_size]);
        if (ee_status != EE_OK)
        {
           if(ee_status == EE_CLEAN_NEEDED) /* Shall not be there if CFG_EE_AUTO_CLEAN = 1*/
           {
              APP_DBG("CLEAN NEEDED, CLEANING");
			  ee_status = EE_Clean(0,0);
           }
           if (ee_status != EE_OK)
           {
              APP_DBG("APP_ZIGBEE_NVM_Write failed @ %d status %d", local_current_size,ee_status);
              break;
           }
        }
		cache_diag_reference.U32_data[local_current_size] =
				cache_persistent_data.U32_data[local_current_size];
		words_written++;
    }

    if(ee_status != EE_OK)
    {
       APP_DBG("WRITE STOPPED, need a FLASH ERASE");
       return false;
    }

	/* Length is the commit word and is deliberately written last. */
	if (!persist_reference_valid ||
			(cache_diag_reference.U32_data[0] != cache_persistent_data.U32_data[0])) {
		ee_status = EE_Write(0, ZIGBEE_DB_START_ADDR,
				cache_persistent_data.U32_data[0]);
		if (ee_status == EE_CLEAN_NEEDED) {
			ee_status = EE_Clean(0, 0);
		}
		if (ee_status != EE_OK) {
			APP_DBG("APP_ZIGBEE_NVM_Write failed @ length status %d", ee_status);
			return false;
		}
		cache_diag_reference.U32_data[0] = cache_persistent_data.U32_data[0];
		words_written++;
	}

	persist_reference_words = num_words;
	persist_reference_valid = true;
	persistNumWordsWritten += words_written;

    APP_DBG("WRITTEN PERSISTENT DATA LEN = %d, changed words = %d, total words = %u",
			cache_persistent_data.U32_data[0], words_written, persistNumWordsWritten);
    return true;

} /* APP_ZIGBEE_NVM_Write */

/**
 * @brief  Erase the NVM
 * @param  None
 * @retval None
 */
static void APP_ZIGBEE_NVM_Erase(void)
{
   nvm_ready = (EE_Init(1, HW_FLASH_ADDRESS + CFG_NVM_BASE_ADDRESS) == EE_OK); /* Erase Flash */
	persist_reference_valid = false;
	persist_reference_words = 0U;
	memset(&zigbee_diag, 0, sizeof(zigbee_diag));
	zigbee_diag.magic = APP_ZIGBEE_DIAG_MAGIC;
	zigbee_diag.version = APP_ZIGBEE_DIAG_VERSION;
	diag_dirty = nvm_ready;
} /* APP_ZIGBEE_NVM_Erase */

#endif /* CFG_NVM */


static void zb_leave_cb(struct ZbNlmeLeaveConfT *conf, void *arg)
{
	struct zigbee_app_info *app = (struct zigbee_app_info *)arg;
	ZbReset(app->zb);

	/* Configure the joining parameters */
	zigbee_app_info.join_delay = HAL_GetTick(); /* now */
	zigbee_app_info.startupControl = ZbStartTypeJoin;

	/* attempt to reconnect */
	UTIL_SEQ_SetTask(1U << CFG_TASK_ZIGBEE_NETWORK_FORM, CFG_SCH_PRIO_0);

}

void ZIGBEE_Leave(void)
{
	enum ZbStatusCodeT status =
			ZbLeaveReq(zigbee_app_info.zb, zb_leave_cb, &zigbee_app_info);

	zigbee_app_info.join_status = (enum ZbStatusCodeT) 0x01; /* init to error status */

	if (ZB_STATUS_SUCCESS == status) {
		APP_ZIGBEE_persist_delete();
	}
}

enum ZbStatusCodeT ZIGBEE_JoinStatus(void)
{
		return zigbee_app_info.join_status;
}

/* USER CODE END FD_LOCAL_FUNCTIONS */
