David-EIPI/stm32-zigbee-light/firmware/STM32_WPAN/App/app_zigbee.h

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
/* Define to prevent recursive inclusion -------------------------------------*/
#ifndef APP_ZIGBEE_H
#define APP_ZIGBEE_H

#ifdef __cplusplus
extern "C" {
#endif

/* Includes ------------------------------------------------------------------*/
#include "tl.h"
#include "tl_zigbee_hci.h"

/* Exported types ------------------------------------------------------------*/

/* Application errors                 */
/*------------------------------------*/

/*
 *  List of all errors tracked by the Zigbee application
 *  running on M4. Some of these errors may be fatal
 *  or just warnings
 */
typedef enum
{
  ERR_ZIGBE_CMD_TO_M0,
  ERR_ZIGBEE_CHECK_WIRELESS
} ErrAppliIdEnum_t;
/* Exported constants --------------------------------------------------------*/

/* External variables --------------------------------------------------------*/
/* Exported macros ------------------------------------------------------------*/
/* Exported functions ------------------------------------------------------- */
void APP_ZIGBEE_Init(void);
void APP_ZIGBEE_Error(uint32_t ErrId, uint32_t ErrCode);
void APP_ZIGBEE_RegisterCmdBuffer(TL_CmdPacket_t *p_buffer);
void APP_ZIGBEE_TL_INIT(void);
void Pre_ZigbeeCmdProcessing(void);
/* USER CODE BEGIN EF */
void ZIGBEE_Leave(void);
enum ZbStatusCodeT ZIGBEE_JoinStatus(void);
void APP_ZIGBEE_update_illum(uint16_t illum);
void APP_ZIGBEE_update_lightstate(uint16_t state);
void APP_ZIGBEE_update_motion_detect(uint16_t state);
void APP_ZIGBEE_update_dusk_detect(uint16_t state);
void APP_ZIGBEE_update_temperature(int16_t temp);

/* USER CODE END EF */
#ifdef __cplusplus
} /* extern "C" */
#endif

#endif /* APP_ZIGBEE_H */
